Luc3as/Smart-Indoor-Greenhouse/Lovelace-card-resources/background.png

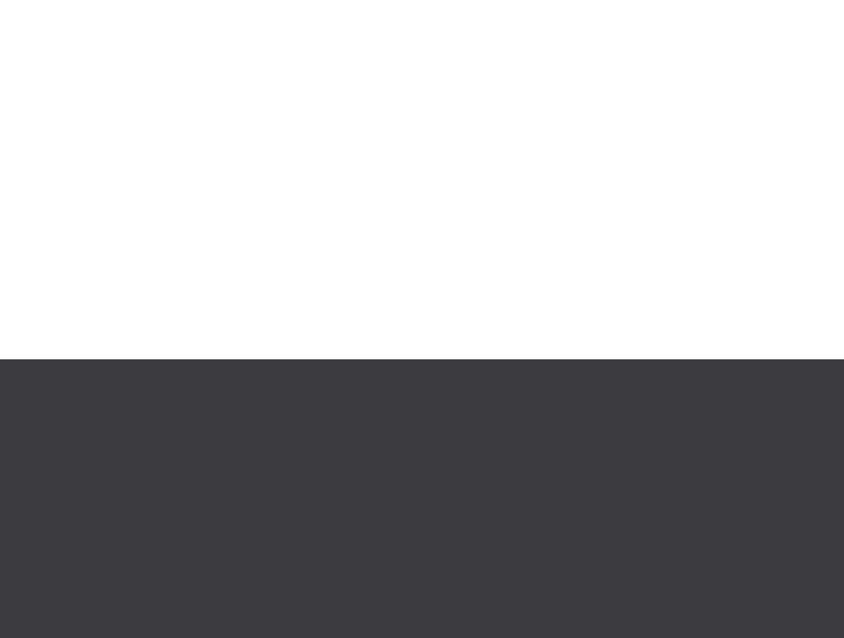
Lovelace-card-resources/background.png
