Luc3as/Smart-Indoor-Greenhouse/Lovelace-card-resources/circle.png

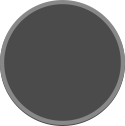
Lovelace-card-resources/circle.png
