Luc3as/Smart-Indoor-Greenhouse/PCB/Smart-greenhouse-controller-scheme.jpg

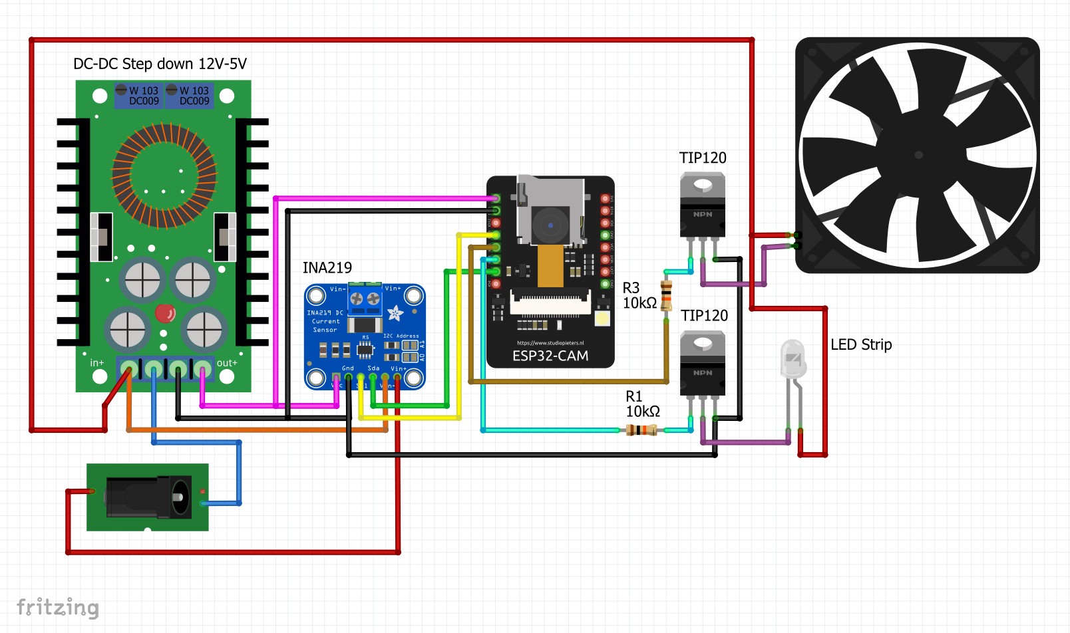
PCB/Smart-greenhouse-controller-scheme.jpg
