Luc3as/Smart-Indoor-Greenhouse/Photos/Camera-case-render (1).png

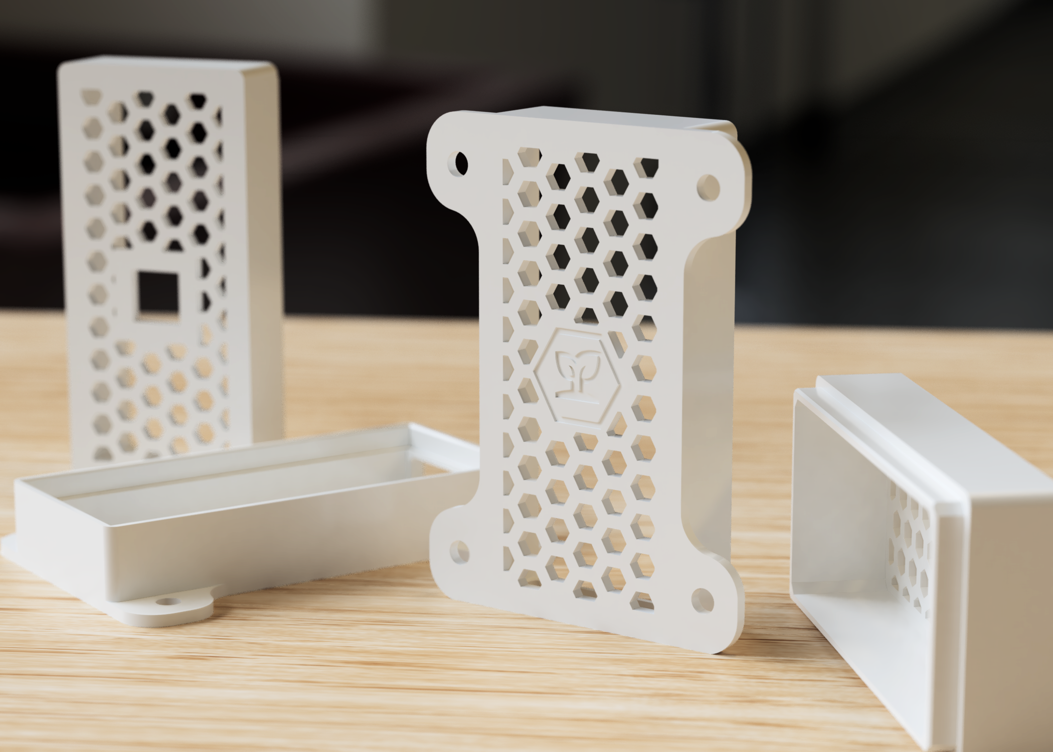
Photos/Camera-case-render (1).png
