Luc3as/Smart-Indoor-Greenhouse/Photos/Greenhouse-controller (4).jpg

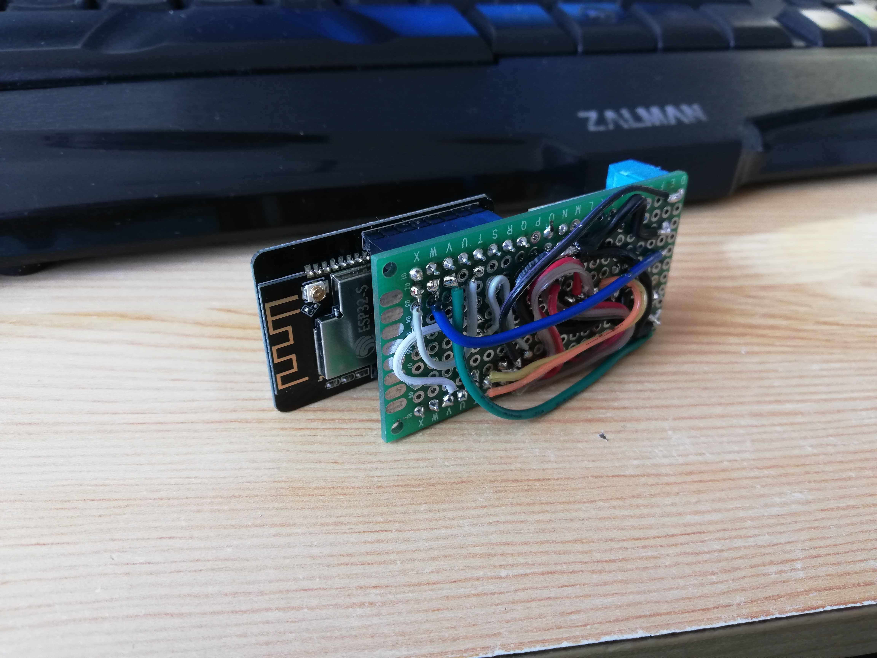
Photos/Greenhouse-controller (4).jpg
