Luc3as/Smart-Indoor-Greenhouse/Photos/Greenhouse-render (2).png

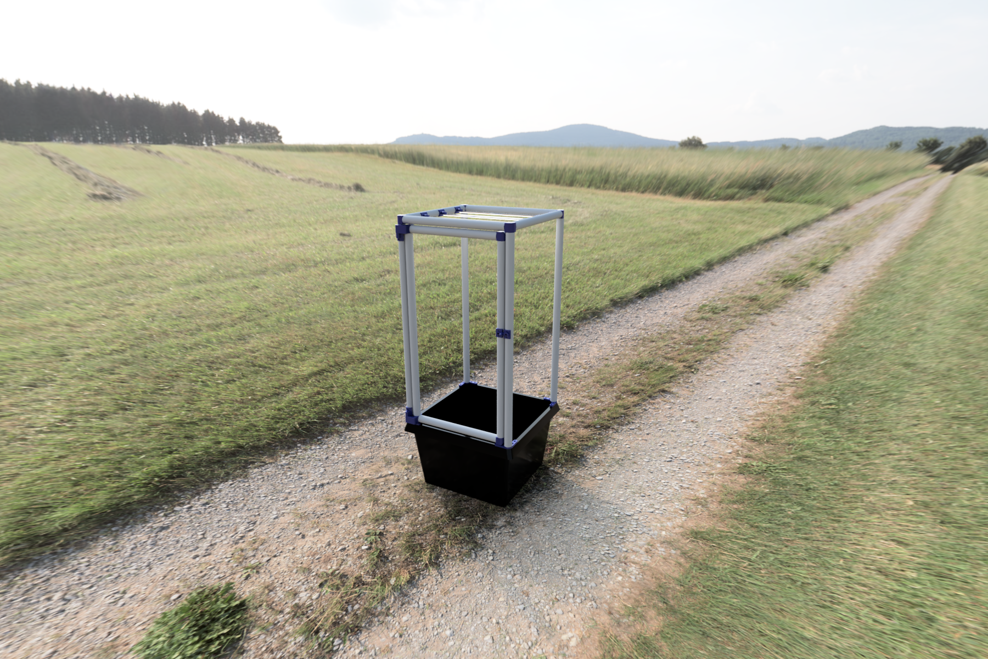
Photos/Greenhouse-render (2).png
