Luc3as/Smart-Indoor-Greenhouse/Photos/Lovelace-card.jpg

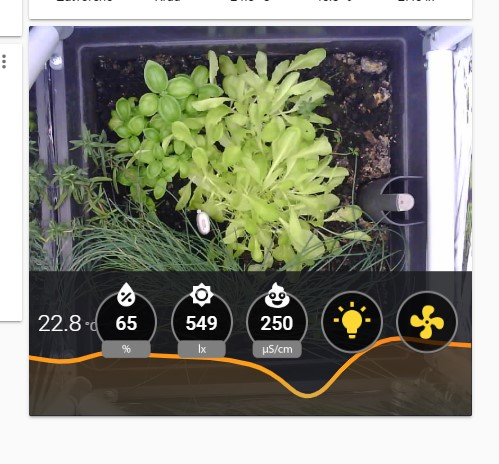
Photos/Lovelace-card.jpg
