Luc3as/Smart-Indoor-Greenhouse/Photos/Greenhouse-build (3).jpg

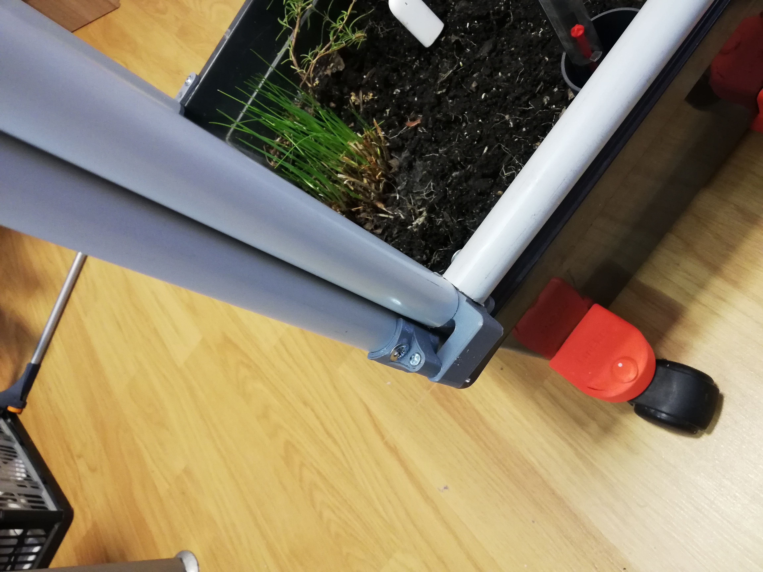
Photos/Greenhouse-build (3).jpg
