Luc3as/Smart-Indoor-Greenhouse/Photos/Greenhouse-build (4).jpg

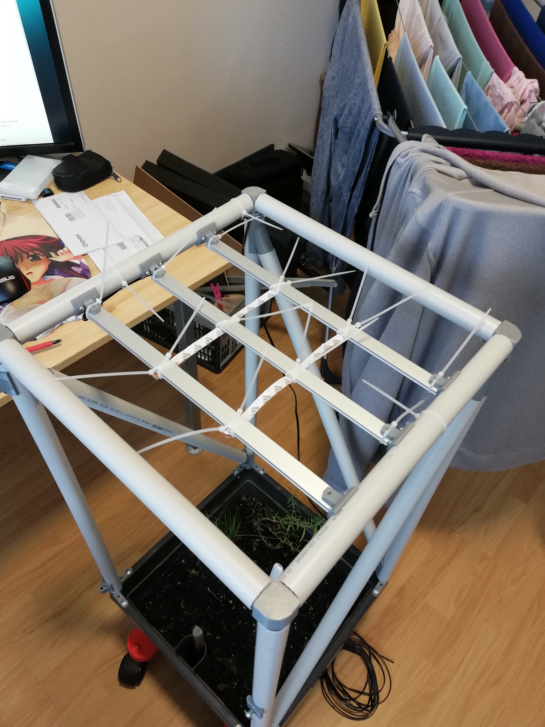
Photos/Greenhouse-build (4).jpg
