Luc3as/Smart-Indoor-Greenhouse/Photos/Greenhouse-build (5).jpg

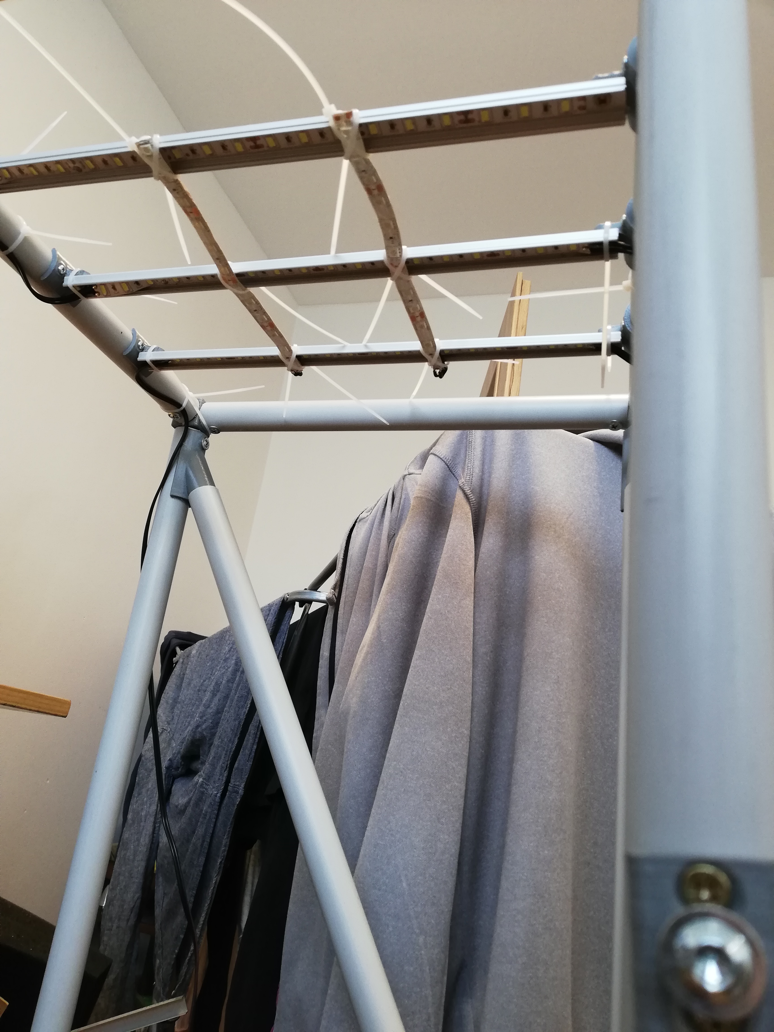
Photos/Greenhouse-build (5).jpg
