Luc3as/Smart-Indoor-Greenhouse/Photos/Greenhouse-build (6).jpg

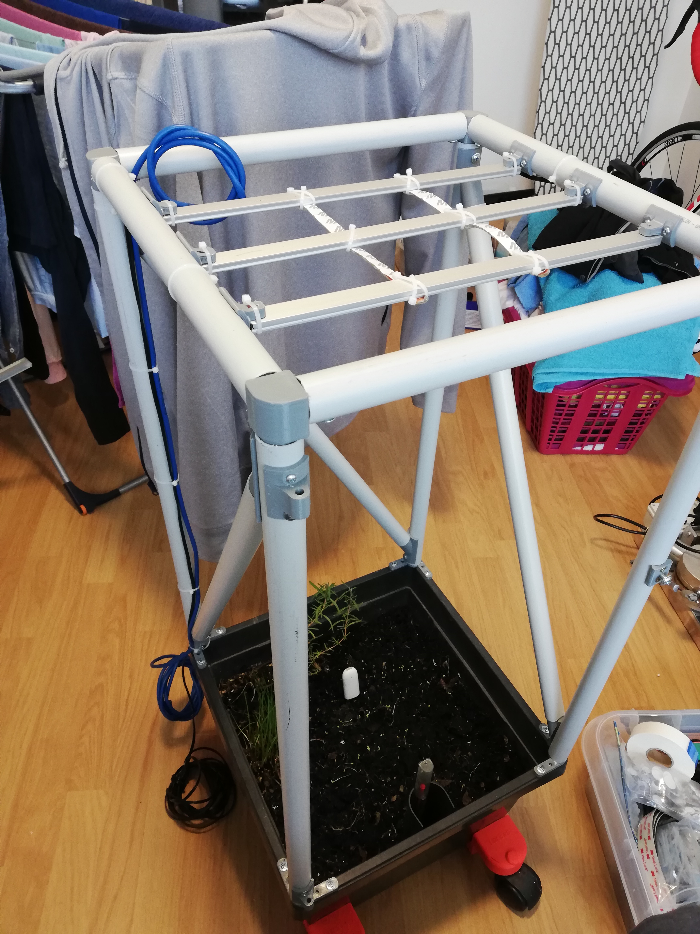
Photos/Greenhouse-build (6).jpg
