Luc3as/Smart-Indoor-Greenhouse/Photos/Greenhouse-build (8).jpg

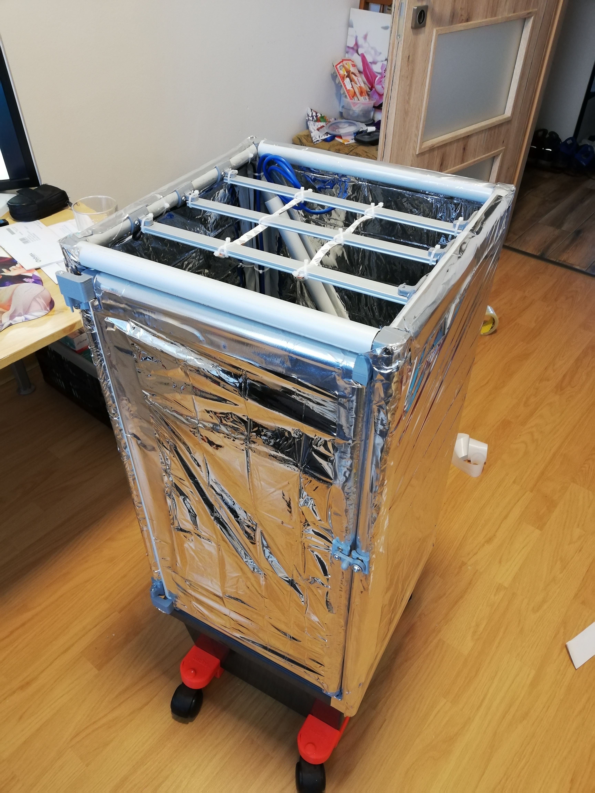
Photos/Greenhouse-build (8).jpg
